iotlibre/Ecohouse/EmonESP/docs/admin.png

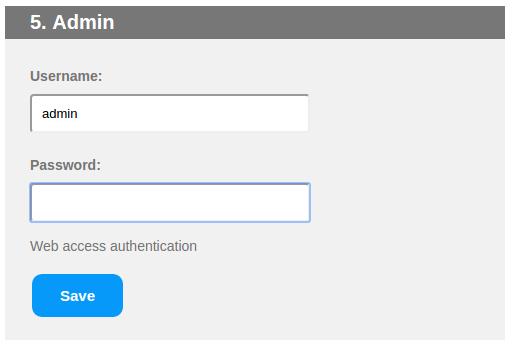
EmonESP/docs/admin.png
