iotlibre/Ecohouse/EmonESP/docs/emoncms.png

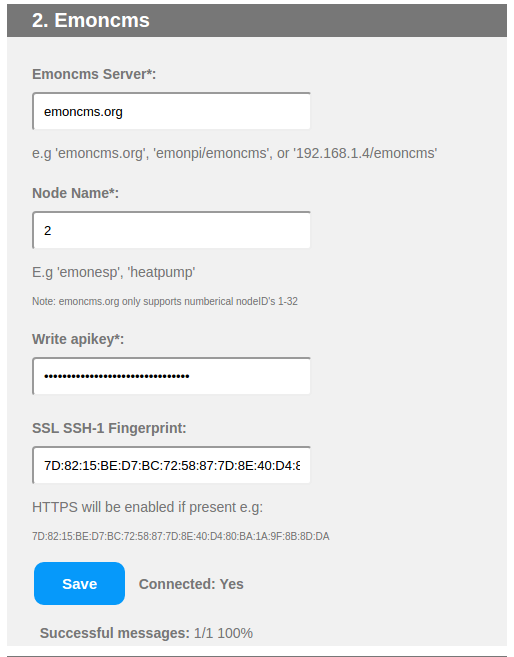
EmonESP/docs/emoncms.png
