iotlibre/Ecohouse/EmonESP/docs/emonesp.png

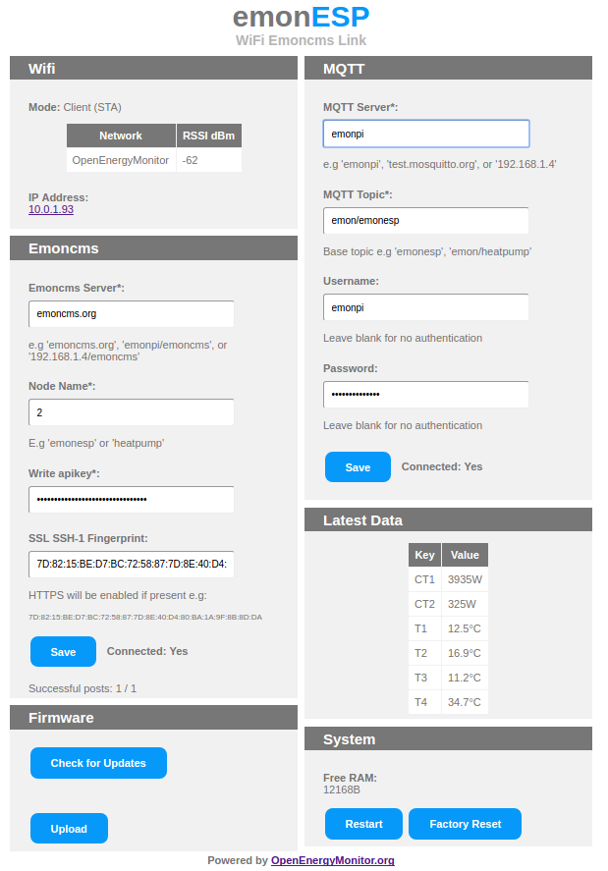
EmonESP/docs/emonesp.png
