iotlibre/Ecohouse/EmonESP/docs/input.png

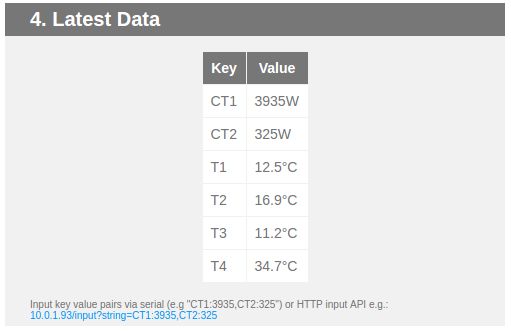
EmonESP/docs/input.png
