iotlibre/Ecohouse/EmonESP/docs/mqtt.png

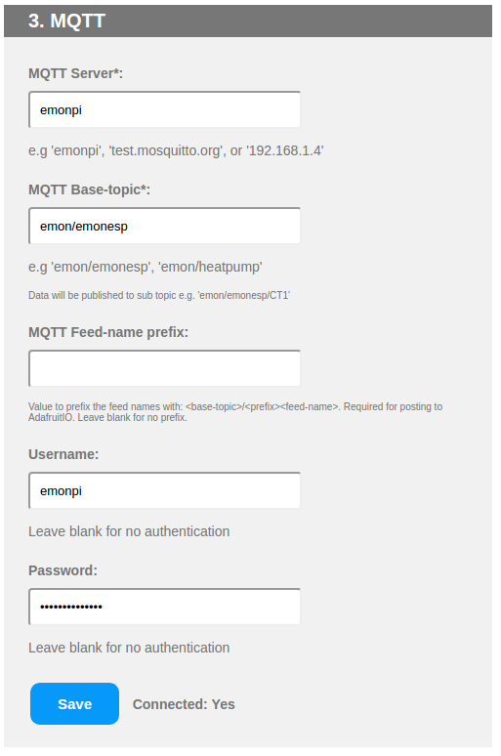
EmonESP/docs/mqtt.png
