iotlibre/Ecohouse/EmonESP/docs/system.png

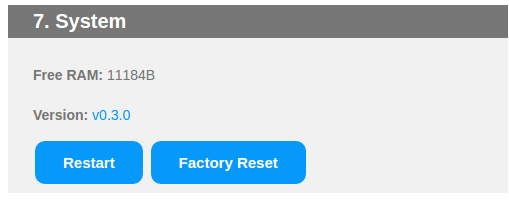
EmonESP/docs/system.png
