iotlibre/Ecohouse/EmonESP/docs/wifi-scan.png

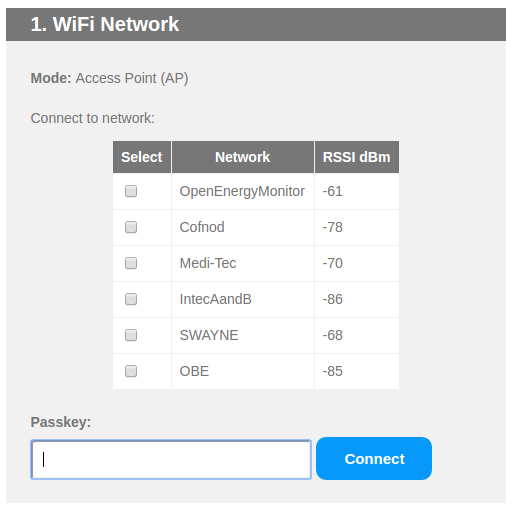
EmonESP/docs/wifi-scan.png
