iotlibre/Ecohouse/EmonESP/docs/wifi.png

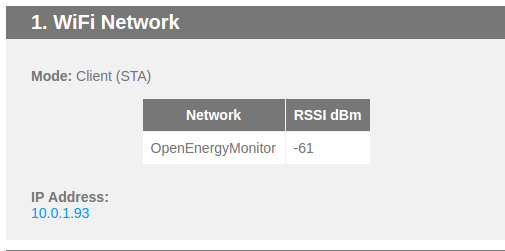
EmonESP/docs/wifi.png
